lucassperanzini/CP4-MakerLab/src/Carrinho/hobbits.ino

// Can be moved in header file i.e notes.h
#define ARRAY_LEN(array) (sizeof(array) / sizeof(array[0]))
#define D5 587
#define E5 659
#define Fb5 740
#define A5 880
#define B5 988
#define A4 440
#define B4 494
#define Cb5 554
#define Fb4 370
#define E4 330
#define G4 392
#define D4 294
#define Cb4 277
#define Gb5 831
#define Ab5 932
#define B3 247
#define G5 784
#define Cb6 1109
#define D6 1175

const int midi3[279][3] = {
 {D5, 144, 0},
 {E5, 144, 0},
 {Fb5, 144, 1010},
 {Fb5, 144, 433},
 {Fb5, 144, 144},
 {A5, 72, 0},
 {B5, 72, 0},
 {A5, 72, 72},
 {E5, 144, 144},
 {D5, 144, 144},
 {E5, 144, 1298},
 {A4, 144, 0},
 {B4, 144, 0},
 {Cb5, 144, 433},
 {Cb5, 433, 144},
 {D5, 144, 433},
 {B4, 144, 144},
 {Fb4, 144, 721},
 {A4, 144, 144},
 {E4, 144, 1587},
 {A4, 144, 144},
 {Cb5, 144, 144},
 {D5, 144, 0},
 {E5, 144, 0},
 {Fb5, 144, 433},
 {Fb5, 144, 1010},
 {A5, 144, 144},
 {Fb5, 144, 144},
 {E5, 144, 433},
 {D5, 144, 144},
 {E5, 144, 144},
 {Cb5, 144, 433},
 {D5, 144, 0},
 {Cb5, 144, 0},
 {B4, 2308, 0},
 {D5, 865, 0},
 {Cb5, 1154, 0},
 {B4, 144, 144},
 {Fb4, 721, 144},
 {G4, 144, 0},
 {Fb4, 144, 0},
 {E4, 865, 0},
 {D4, 144, 0},
 {E4, 144, 0},
 {D4, 1875, 144},
 {Fb4, 144, 0},
 {G4, 144, 0},
 {Cb4, 1154, 0},
 {E4, 1154, 0},
 {D5, 144, 0},
 {E5, 144, 0},
 {Fb5, 144, 1010},
 {Fb5, 144, 433},
 {Fb5, 144, 144},
 {E5, 144, 0},
 {Fb5, 144, 0},
 {Gb5, 144, 433},
 {Gb5, 144, 433},
 {Gb5, 144, 433},
 {Gb5, 144, 144},
 {Fb5, 144, 0},
 {Gb5, 144, 0},
 {Ab5, 144, 721},
 {Cb5, 144, 144},
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
       digitalWrite(led, HIGH); 
    }

    // Espera a duração inteira da nota soar
    delay(noteDuration);
    noTone(pin);

     digitalWrite(led, LOW); 

    // Se houver uma pausa extra definida na matriz, aplica aqui
    if (pauseDuration > 0) {
      delay(pauseDuration);
    }
  }
 
}
